vinmarshall/Radio-Shack-MIDI-Lights/schematic/4_relays_1.bmp

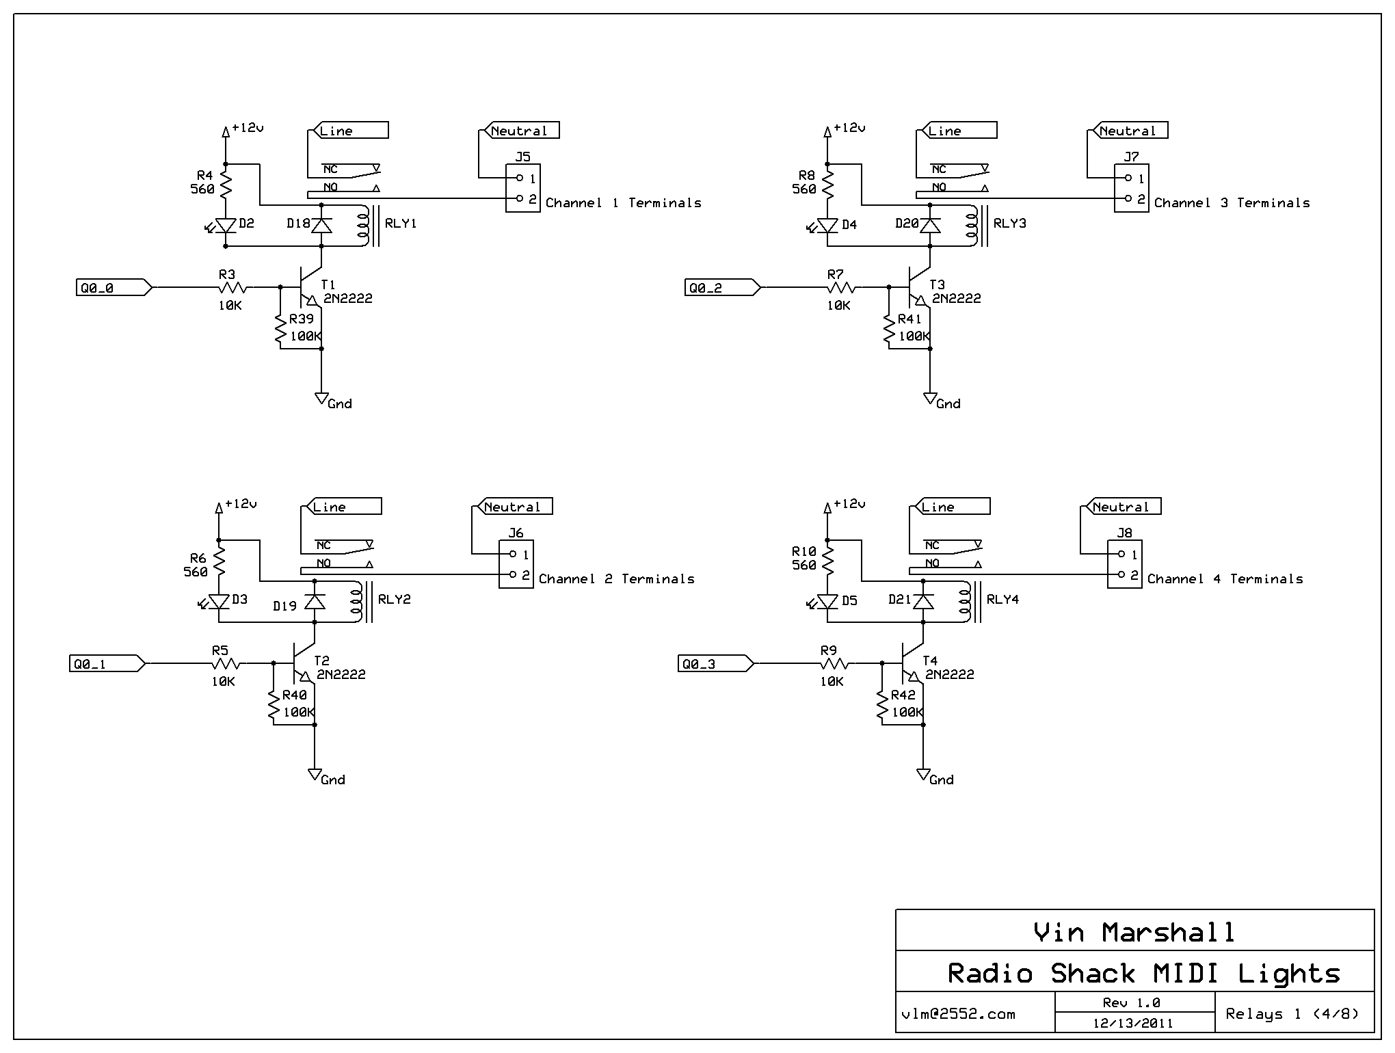
schematic/4_relays_1.bmp
